AlpenglowIndustries/Alpenglow_CircuitBasics/LEDBasics/Kicad Schematic/CircuitAndLEDBasics.kicad_pcb

## KiCad design Hardware/Doc/DDS-915-DIY_Kicad/DDS-915-DIY_Kicad.kicad_sch

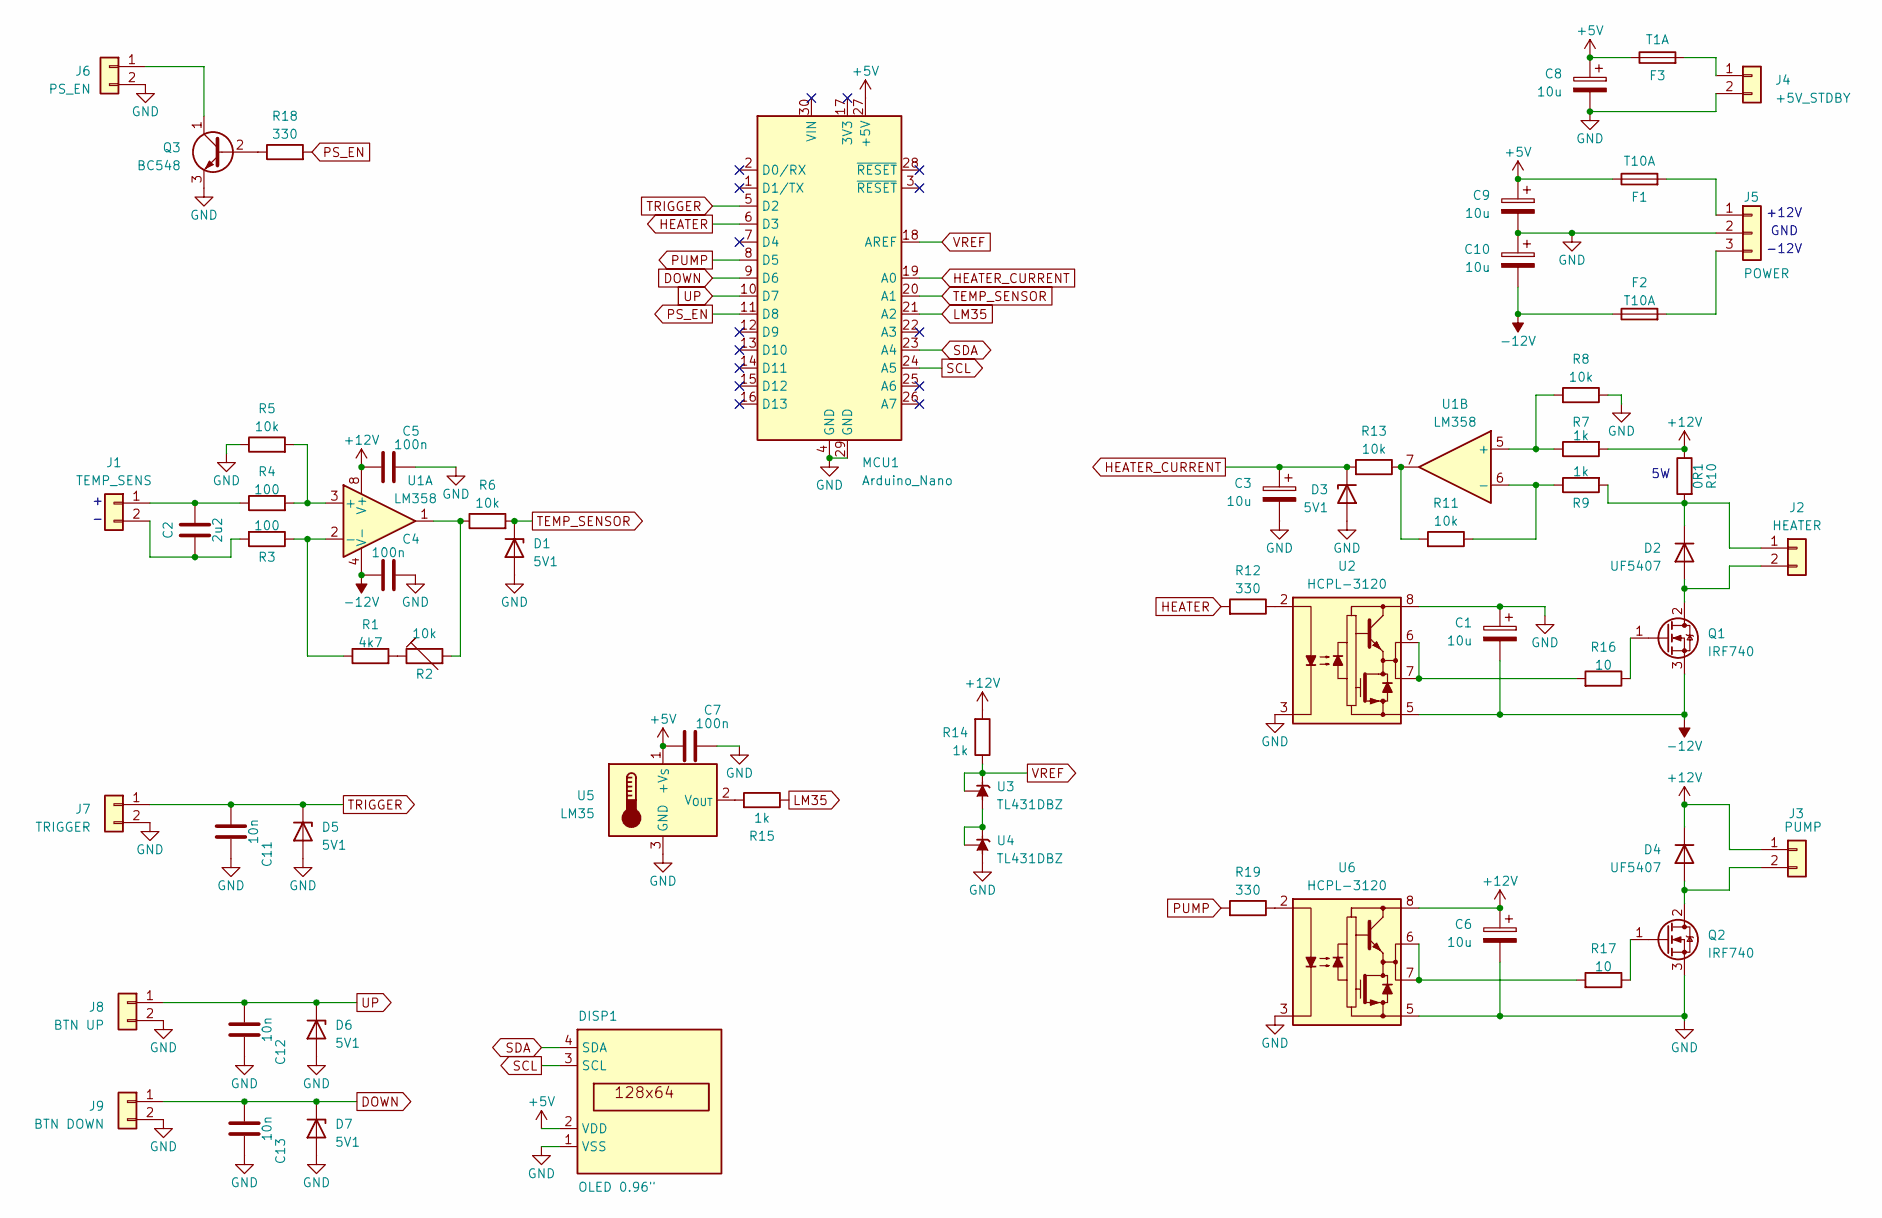
[picture p7: schematic DDS-915-DIY_Kicad.kicad_sch]

Parts:
C1, C3, C6, C8, C9, C10: 10u
C2: 2u2
C4, C5, C7: 100n
C11, C12, C13: 10n
D1, D3, D5, D6, D7: 5V1
D2, D4: UF5407
DISP1: OLED 0.96"
F1, F2: T10A
F3: T1A
J1: TEMP_SENS
J2: HEATER
J3: PUMP
J4: +5V_STDBY
J5: POWER
J6: PS_EN
J7: TRIGGER
J8: BTN UP
J9: BTN DOWN
MCU1: Arduino_Nano
Q1, Q2: IRF740; TO-220-3_Vertical
Q3: BC548; TO-92_Inline
R1: 4k7
R2, R5, R6, R8, R11, R13: 10k
R3, R4: 100
R7, R9, R14, R15: 1k
R10: 0R1
R12, R18, R19: 330
R16, R17: 10
U1: LM358
U2, U6: HCPL-3120; DIP-8_W7.62mm
U3, U4: TL431DBZ; SOT-23
U5: LM35; TO-92_Inline

Connections:
+5V: C7.1, C8.1, C9.1, DISP1.2 (VDD), F1.1, F3.1, MCU1.27 (+5V), U5.1 (+V_{S})
+12V: C5.1, C6.1, D4.1 (K), J3.1, R7.2, R10.1, R14.2, U1.8 (V+), U6.8 (VCC)
-12V: C1.2, C4.1, C10.2, F2.1, Q1.3 (S), U1.4 (V-), U2.5 (VEE)
DOWN: C13.1, D7.1 (K), J9.1, MCU1.9 (D6)
GND: C1.1, C3.2, C4.2, C5.2, C6.2, C7.2, C8.2, C9.2, C10.1, C11.2, C12.2, C13.2, D1.2 (A), D3.2 (A), D5.2 (A), D6.2 (A), D7.2 (A), DISP1.1 (VSS), J4.2, J5.2, J6.2, J7.2, J8.2, J9.2, MCU1.4 (GND), MCU1.29 (GND), Q2.3 (S), Q3.3 (E), R5.1, R8.1, U2.3 (C), U2.8 (VCC), U4.3 (A), U5.3 (GND), U6.3 (C), U6.5 (VEE)
HEATER: MCU1.6 (D3), R12.2
HEATER_CURRENT: C3.1, D3.1 (K), MCU1.19 (A0), R13.2
LM35: MCU1.21 (A2), R15.1
unnamed: C2.1, J1.1, R4.1
unnamed: C2.2, J1.2, R3.2
unnamed: D2.1 (K), J2.1, R9.2, R10.2
unnamed: D2.2 (A), J2.2, Q1.2 (D)
unnamed: D4.2 (A), J3.2, Q2.2 (D)
unnamed: F1.2, J5.1
unnamed: F2.2, J5.3
unnamed: F3.2, J4.1
unnamed: J6.1, Q3.1 (C)
unnamed: Q1.1 (G), R16.1
unnamed: Q2.1 (G), R17.1
unnamed: Q3.2 (B), R18.1
unnamed: R1.1, R3.1, U1.2 (-)
unnamed: R1.2, R2.1
unnamed: R2.2, R6.1, U1.1
unnamed: R4.2, R5.2, U1.3 (+)
unnamed: R7.1, R8.2, U1.5 (+)
unnamed: R9.1, R11.1, U1.6 (-)
unnamed: R11.2, R13.1, U1.7
unnamed: R12.1, U2.2 (A)
unnamed: R15.2, U5.2 (V_{OUT})
unnamed: R16.2, U2.6 (VO), U2.7 (VO)
unnamed: R17.2, U6.6 (VO), U6.7 (VO)
unnamed: R19.1, U6.2 (A)
unnamed: U3.3 (A), U4.1 (K), U4.2 (REF)
PS_EN: MCU1.11 (D8), R18.2
PUMP: MCU1.8 (D5), R19.2
SCL: DISP1.3 (SCL), MCU1.24 (A5)
SDA: DISP1.4 (SDA), MCU1.23 (A4)
TEMP_SENSOR: D1.1 (K), MCU1.20 (A1), R6.2
TRIGGER: C11.1, D5.1 (K), J7.1, MCU1.5 (D2)
UP: C12.1, D6.1 (K), J8.1, MCU1.10 (D7)
VREF: MCU1.18 (AREF), R14.1, U3.1 (K), U3.2 (REF)

Notes on the sheet:
+12V
-12V
GND
